codefresco/Wings60/gallery/IMG_1900.jpeg

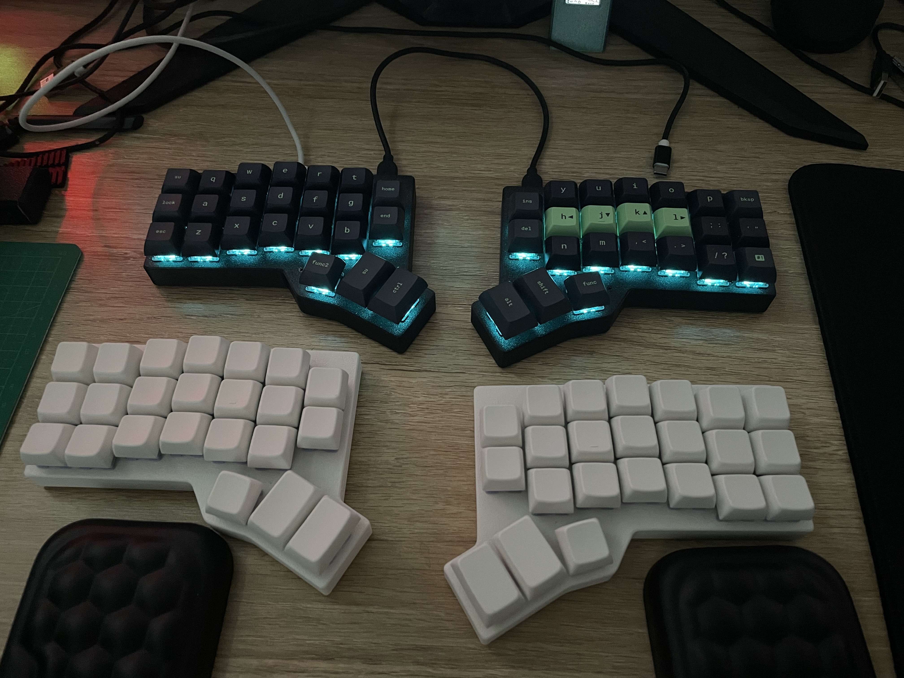
gallery/IMG_1900.jpeg
