codefresco/Wings60/gallery/IMG_2032.jpeg

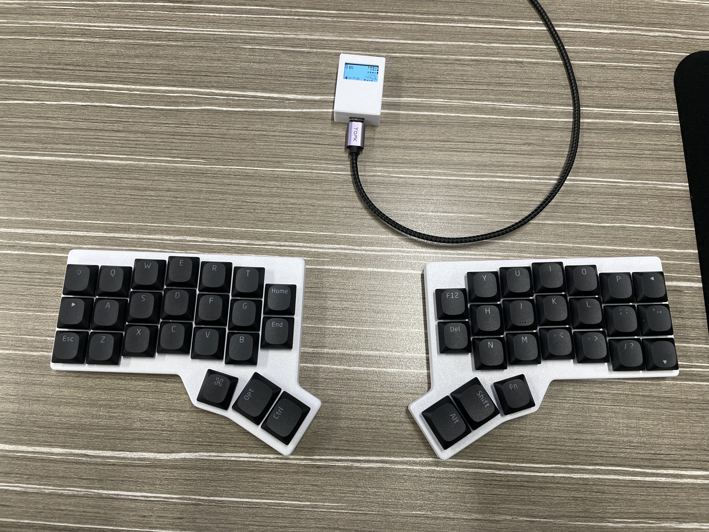
gallery/IMG_2032.jpeg
