codefresco/Wings60/gallery/THChoc.jpeg

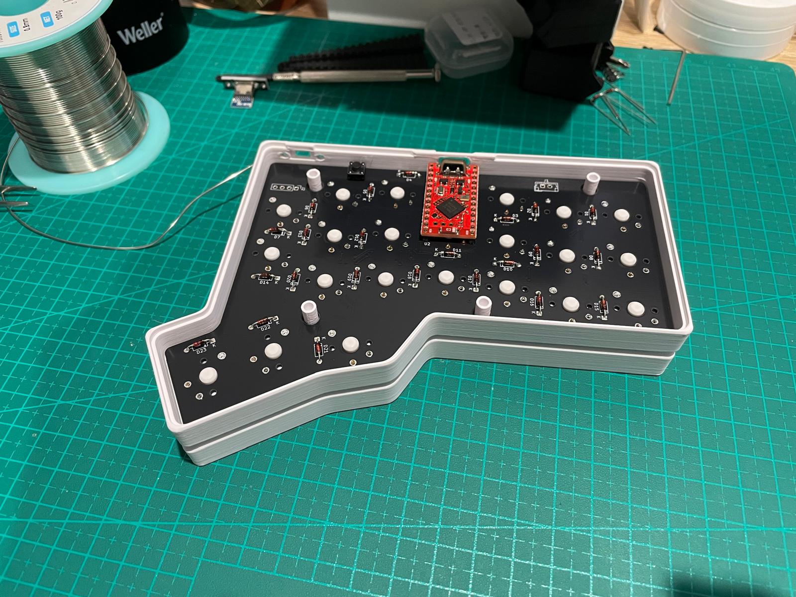
gallery/THChoc.jpeg
