codefresco/Wings60/gallery/wireless_dongle.jpeg

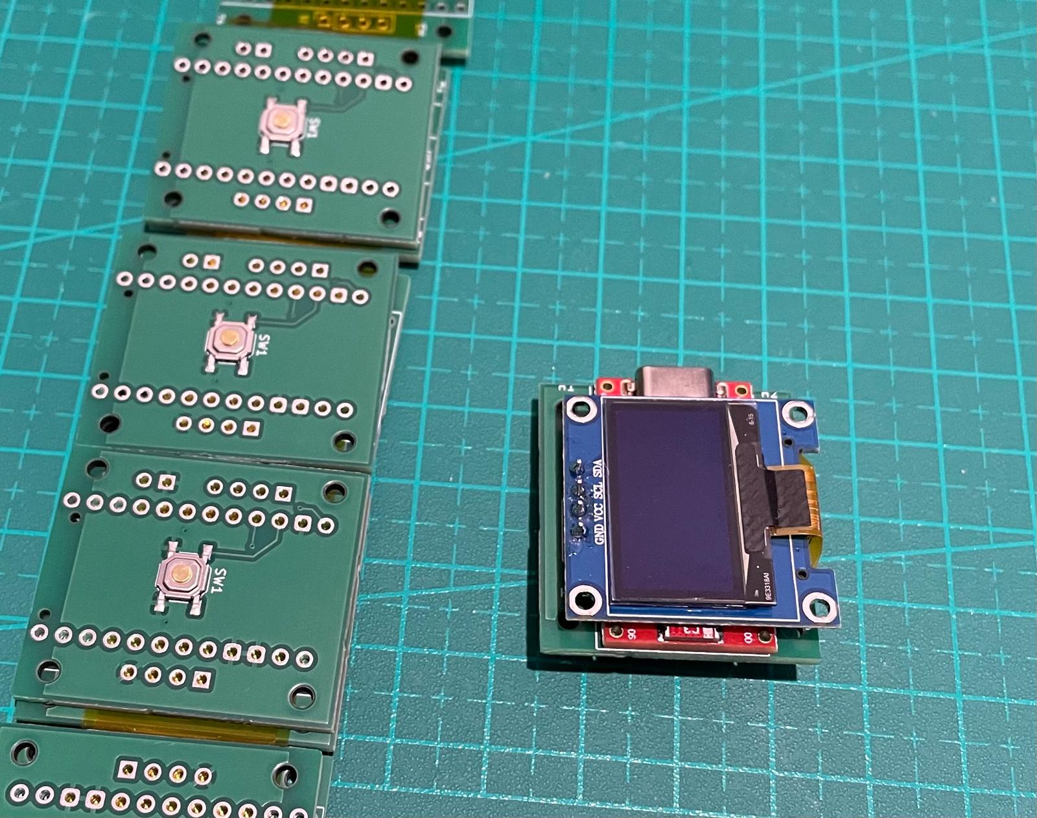
gallery/wireless_dongle.jpeg
