codefresco/Wings60/production/kicad/left/Bottom+null+SMT026041160906.png

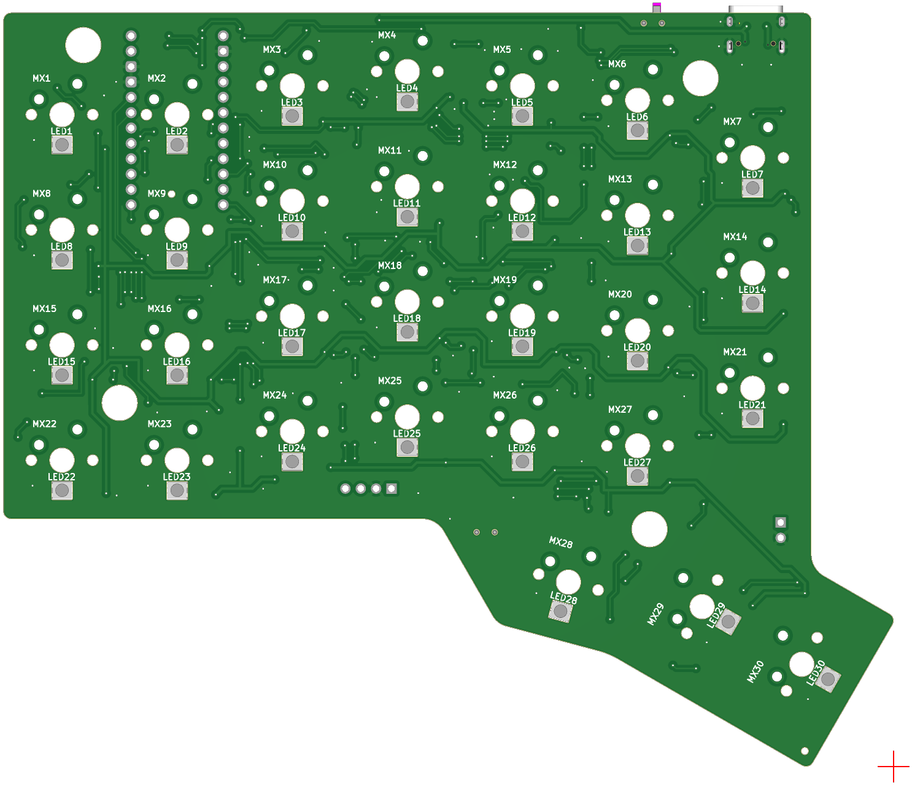
production/kicad/left/Bottom+null+SMT026041160906.png
