codefresco/Wings60/production/kicad/left/left-mcu-facedown.jpg

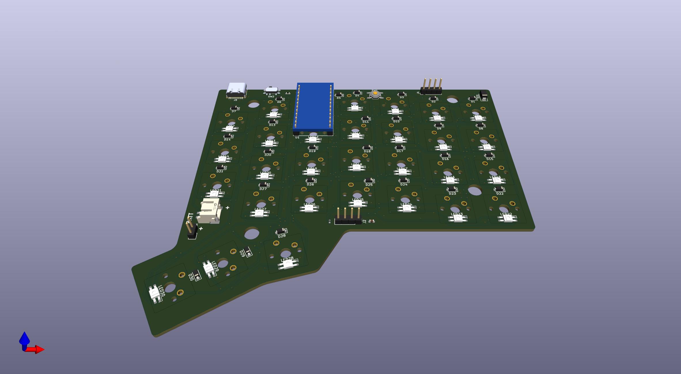
production/kicad/left/left-mcu-facedown.jpg
