codefresco/Wings60/production/kicad/left/left.jpg

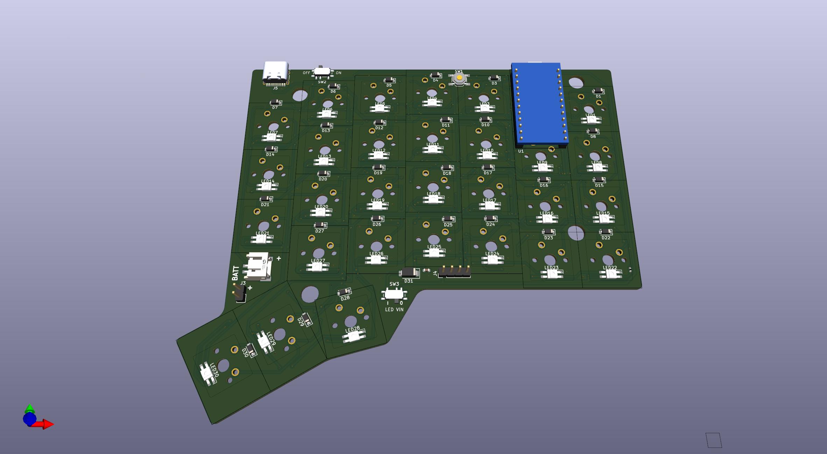
production/kicad/left/left.jpg
