codefresco/Wings60/production/kicad/left/left_barebone_prod.png

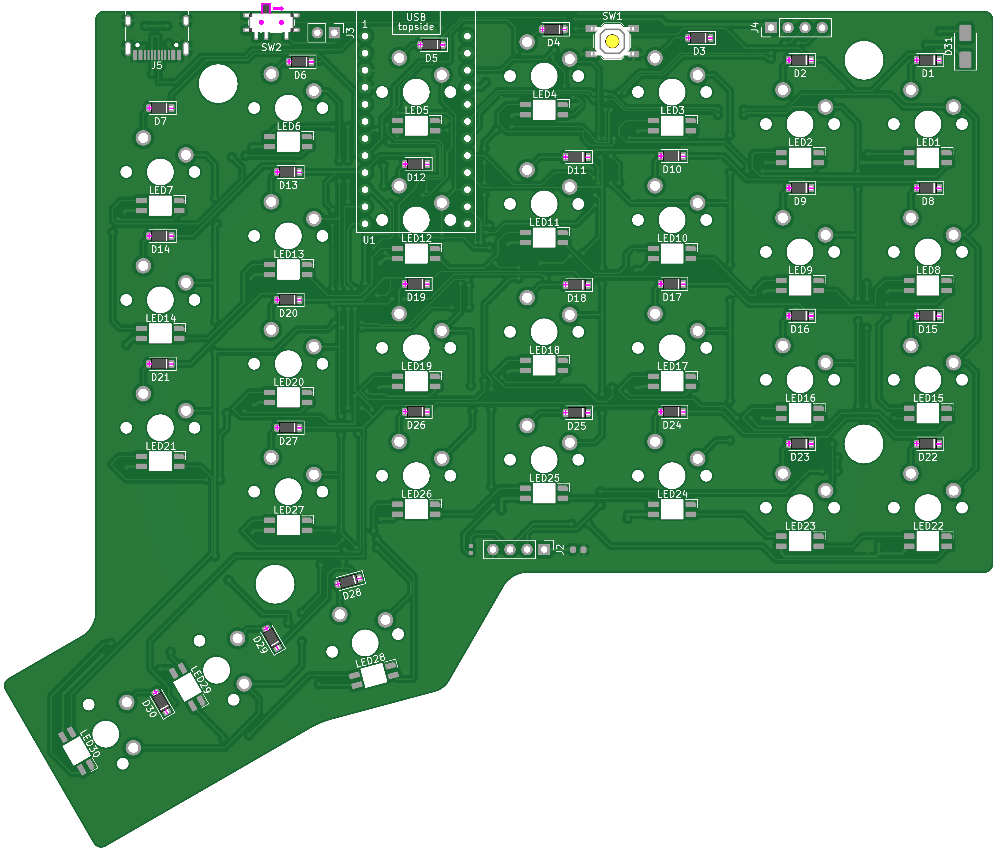
production/kicad/left/left_barebone_prod.png
