codefresco/Wings60/production/kicad/right/right_prod.png

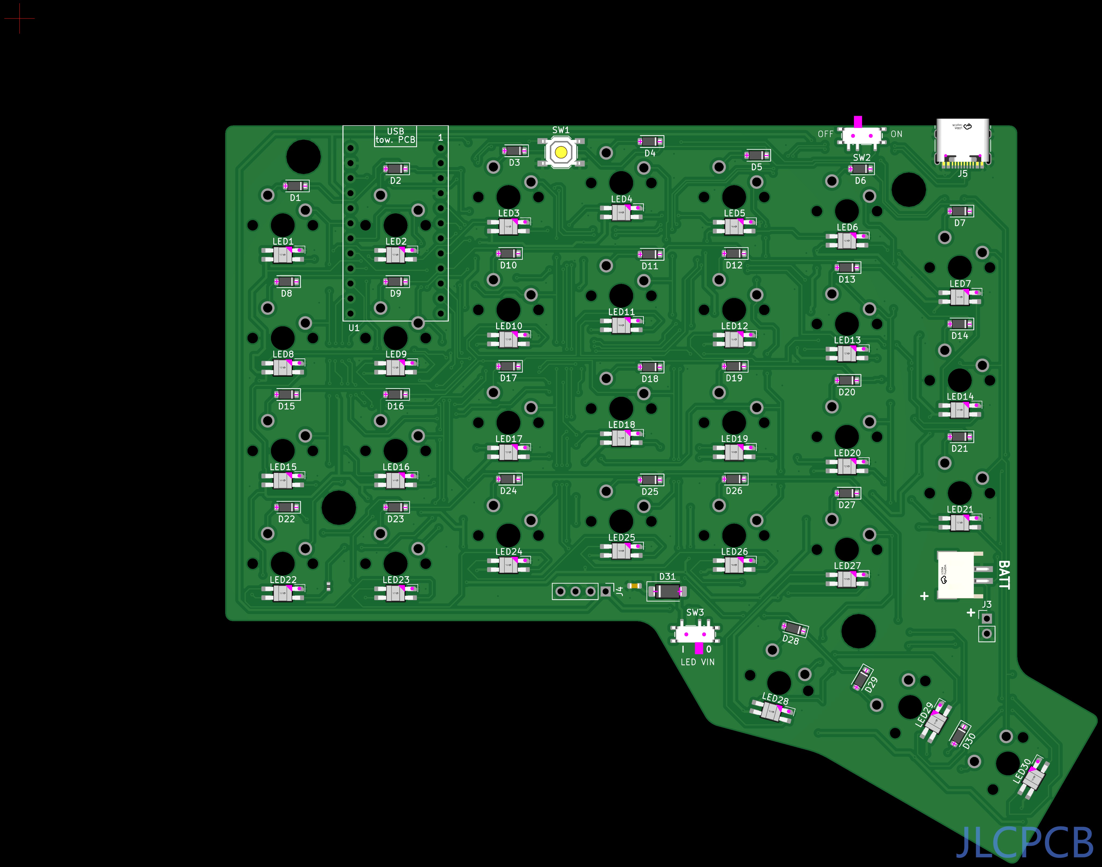
production/kicad/right/right_prod.png
