codefresco/Wings60/production/kicad/right/Top+null+SMT026041160924.png

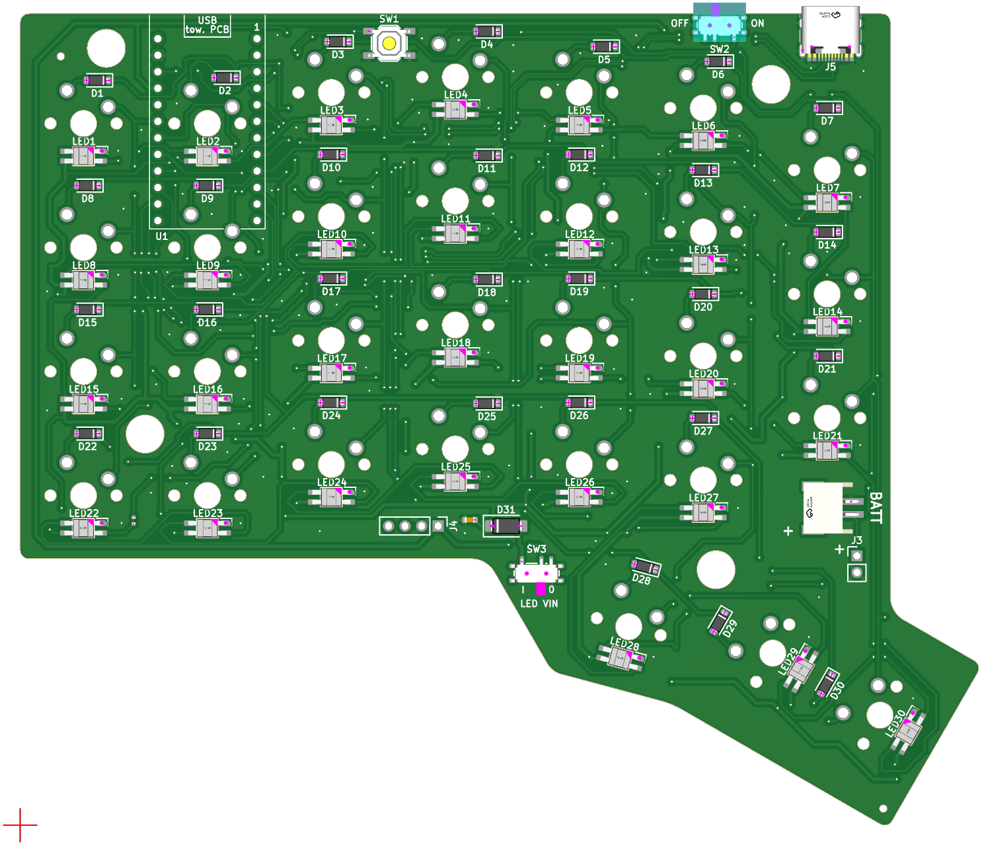
production/kicad/right/Top+null+SMT026041160924.png
